jacobron/EasyHive_M0/V1.3/Hardware/KICAD Board V1.3/PDF/easyhive_1_3_bestückungsplan_bot.pdf

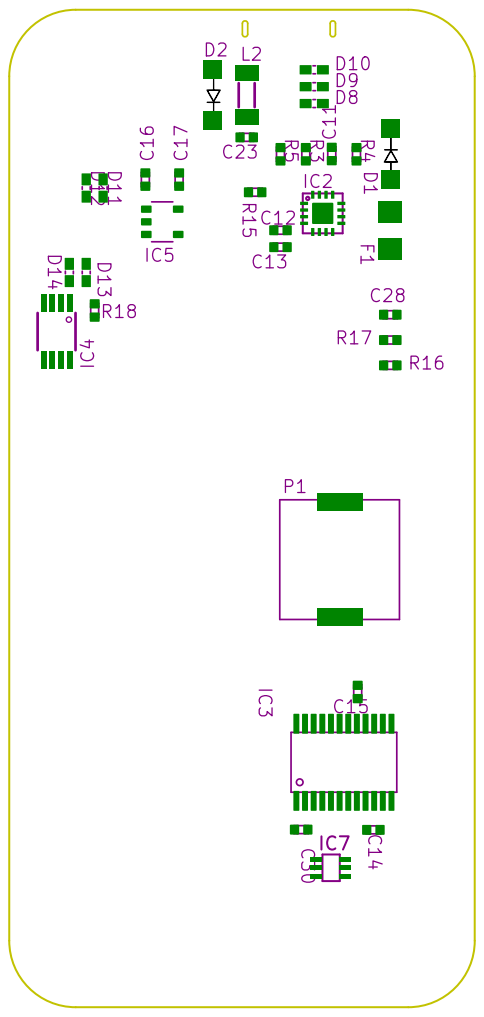
[picture p15: page 1]
