jacobron/EasyHive_M0/V1.2/easyhive_1_2.pdf

# Power Management & Regulator Microcontroller SAM

# Connectors

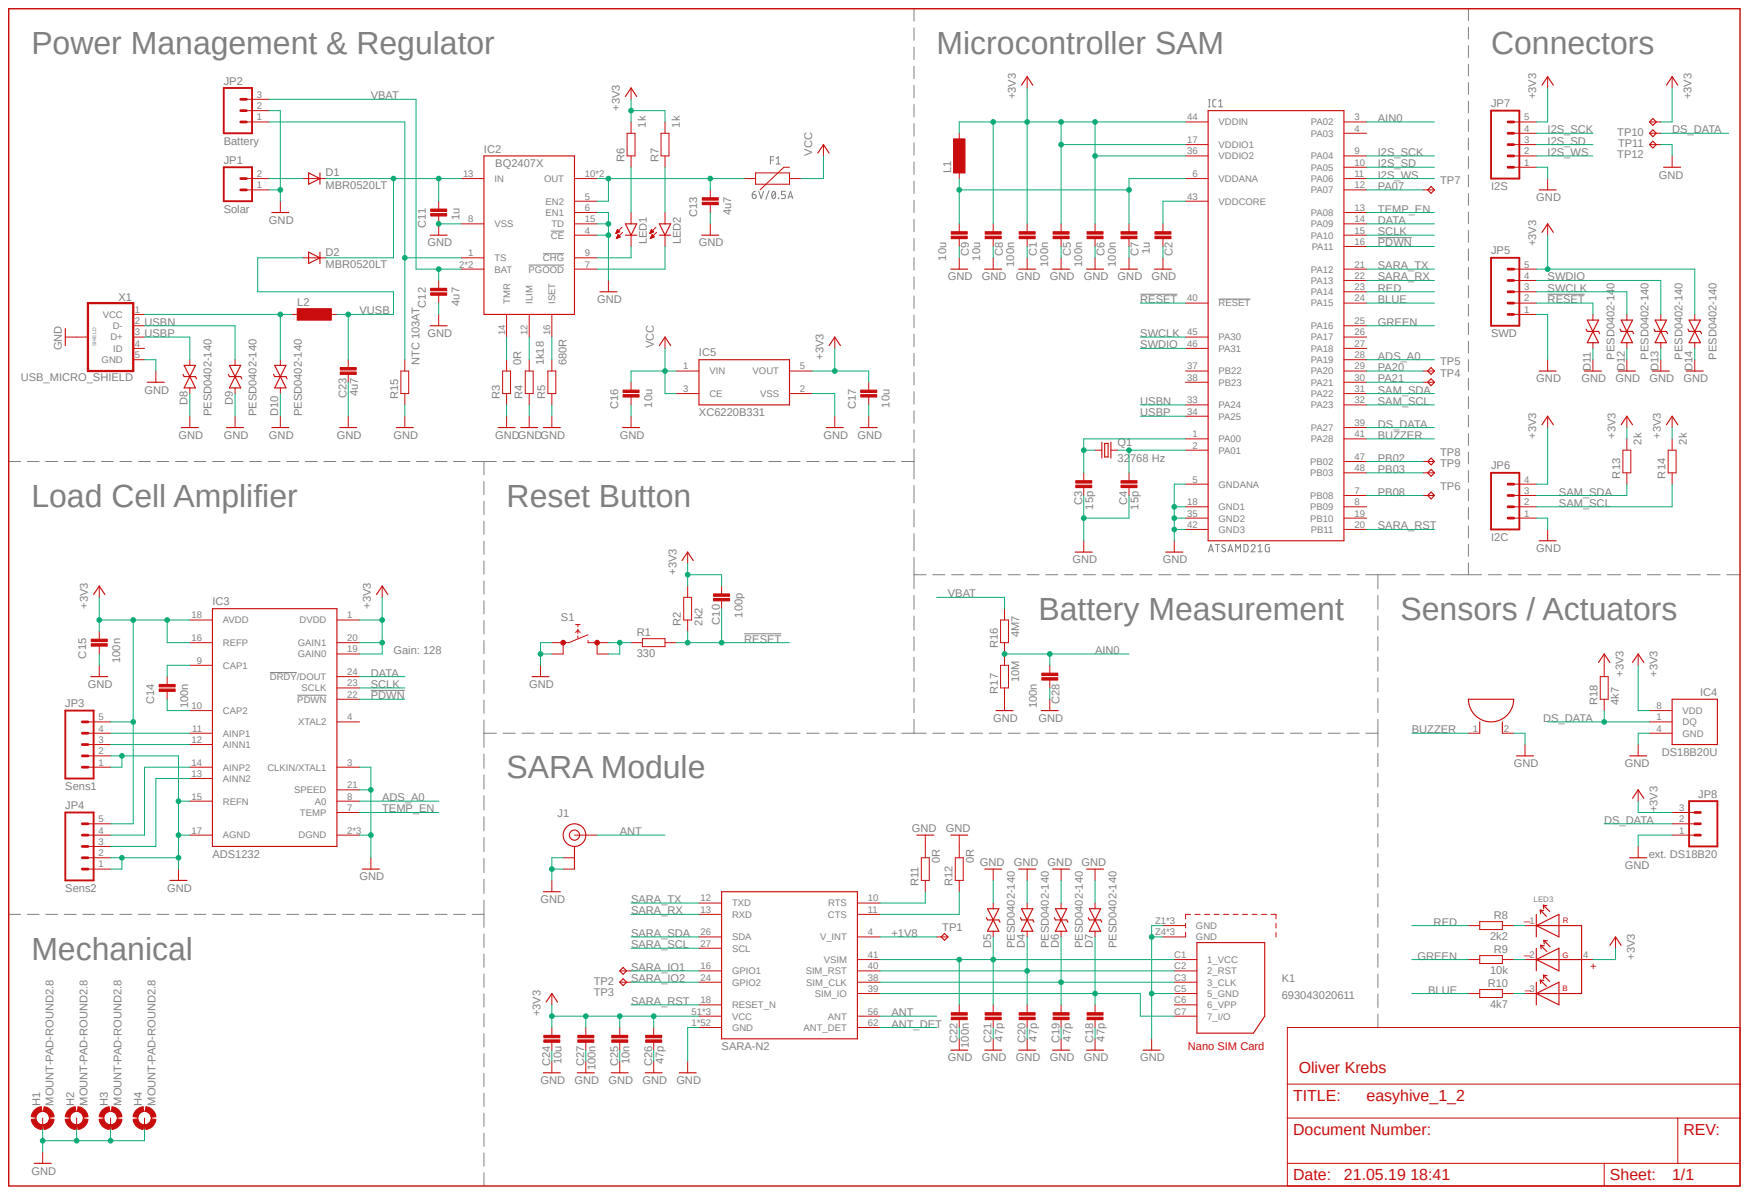
[picture p16: page 1]

GND GND GND GND⁺³V³

VDDIO1 17
VDDIO2 36

VDDCORE 43

3 | AINN1 12
2 | AINP2 14

AINN2 13

GND GND

Document Number: | REV:

Date: 21.05.19 18:41 | Sheet: 1/1
